lucastliu/sciencebot/dev_ws/src/PlotJuggler/docs/images/pj-area-zoom.gif

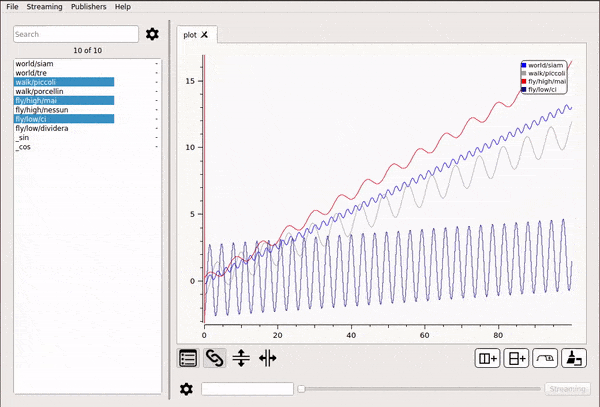
dev_ws/src/PlotJuggler/docs/images/pj-area-zoom.gif
