lucastliu/sciencebot/dev_ws/src/PlotJuggler/docs/images/pj-drag-curve.gif

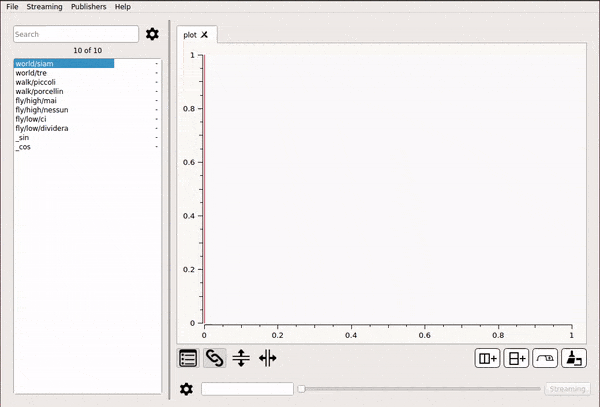
dev_ws/src/PlotJuggler/docs/images/pj-drag-curve.gif
