lucastliu/sciencebot/dev_ws/src/PlotJuggler/docs/images/pj-multiplot.gif

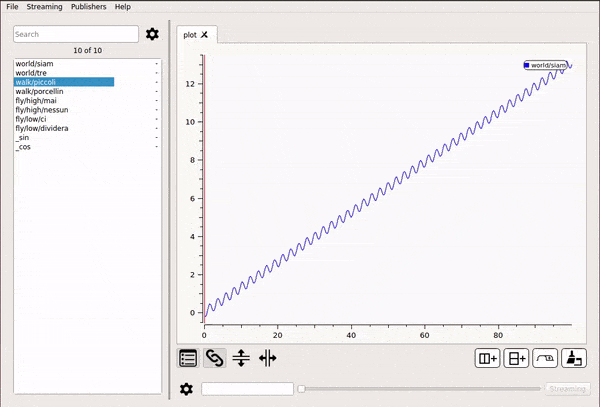
dev_ws/src/PlotJuggler/docs/images/pj-multiplot.gif
