lucastliu/sciencebot/dev_ws/src/PlotJuggler/docs/images/pj-streaming.gif

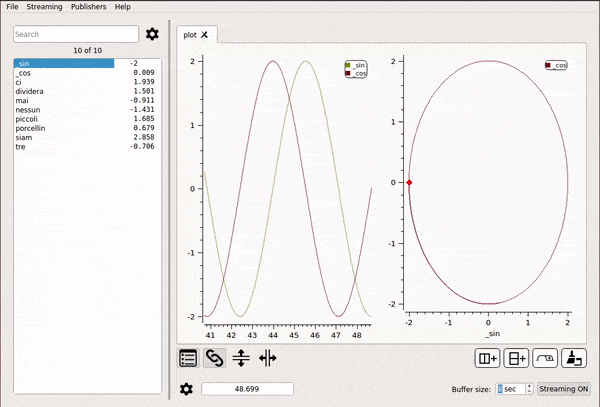
dev_ws/src/PlotJuggler/docs/images/pj-streaming.gif
