lucastliu/sciencebot/dev_ws/src/PlotJuggler/docs/images/pj-streaming.png

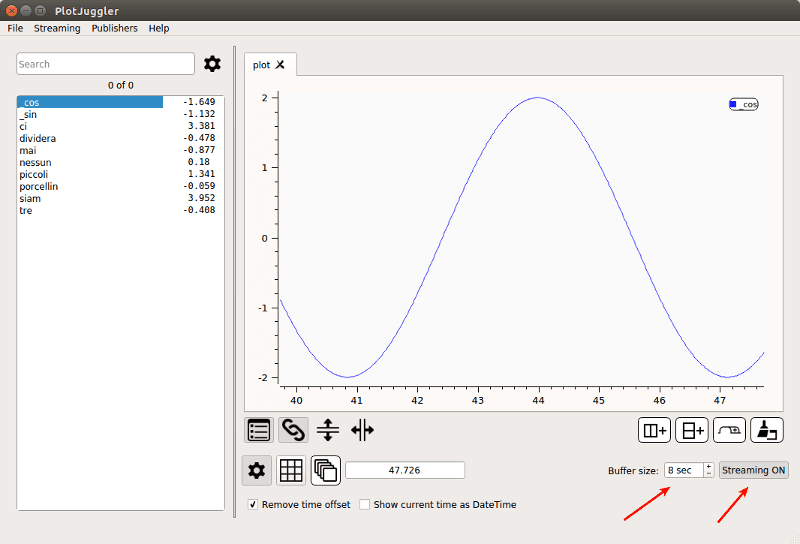
dev_ws/src/PlotJuggler/docs/images/pj-streaming.png
