lucastliu/sciencebot/dev_ws/src/PlotJuggler/docs/images/pj-swap-plots.gif

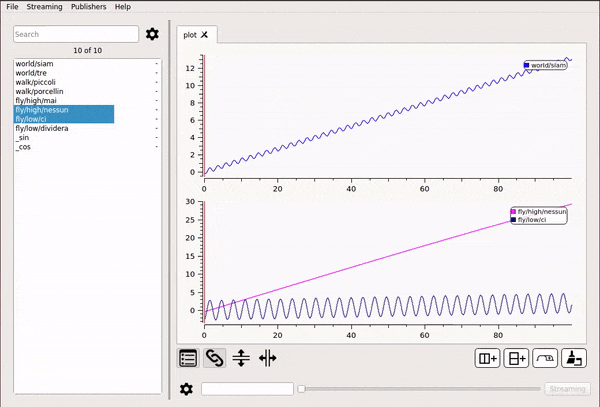
dev_ws/src/PlotJuggler/docs/images/pj-swap-plots.gif
