lucastliu/sciencebot/dev_ws/src/PlotJuggler/docs/images/pj-wheel-zoom.gif

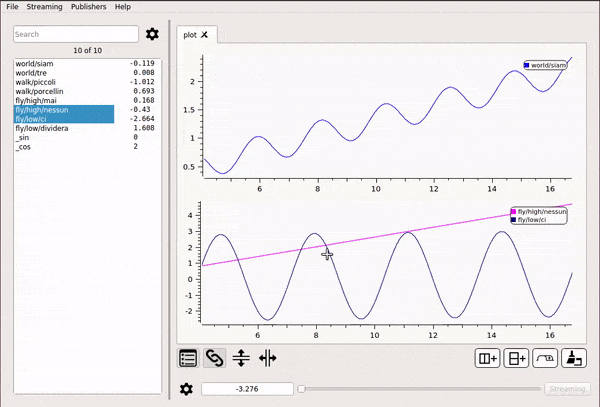
dev_ws/src/PlotJuggler/docs/images/pj-wheel-zoom.gif
