lucastliu/sciencebot/dev_ws/src/PlotJuggler/docs/images/pj-xyplots.gif

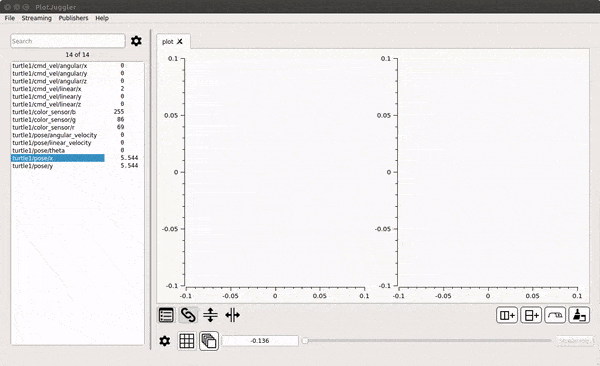
dev_ws/src/PlotJuggler/docs/images/pj-xyplots.gif
