lucastliu/sciencebot/dev_ws/src/PlotJuggler/docs/images/PlotJuggler_terms.png

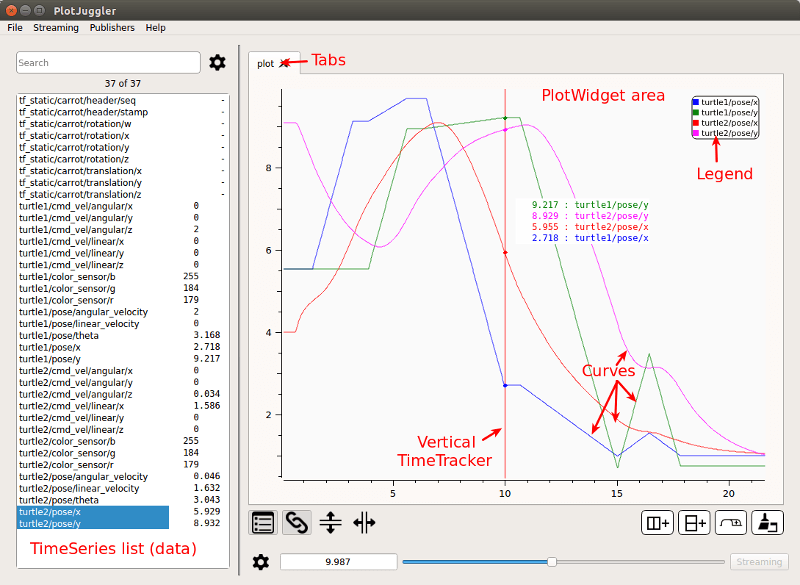
dev_ws/src/PlotJuggler/docs/images/PlotJuggler_terms.png
