lucastliu/sciencebot/dev_ws/src/PlotJuggler/docs/images/PlotJuggler_tracker.png

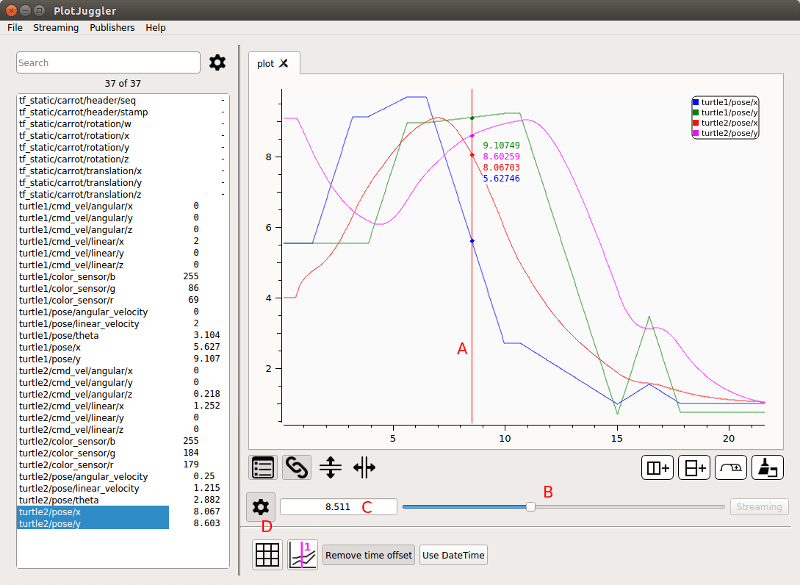
dev_ws/src/PlotJuggler/docs/images/PlotJuggler_tracker.png
