lucastliu/sciencebot/dev_ws/src/PlotJuggler/docs/images/ros-console.png

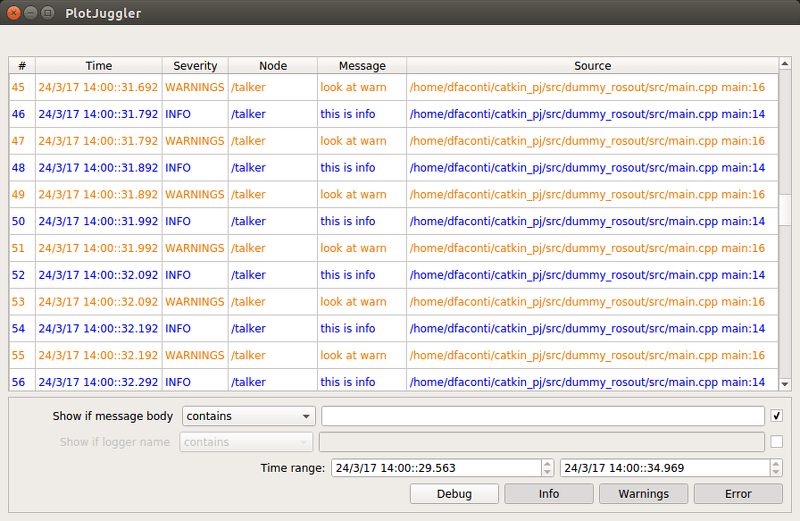
dev_ws/src/PlotJuggler/docs/images/ros-console.png
