lucastliu/sciencebot/dev_ws/src/PlotJuggler/docs/images/ros-topics.png

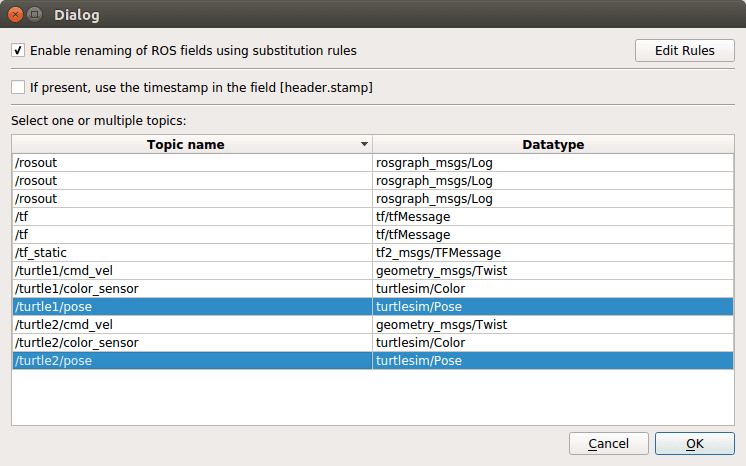
dev_ws/src/PlotJuggler/docs/images/ros-topics.png
