lucastliu/sciencebot/dev_ws/src/PlotJuggler/docs/images/show_me_the_rosbag.jpg

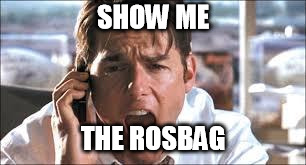
dev_ws/src/PlotJuggler/docs/images/show_me_the_rosbag.jpg
