lucastliu/sciencebot/dev_ws/src/PlotJuggler/plotter_gui/resources/Davide.jpg

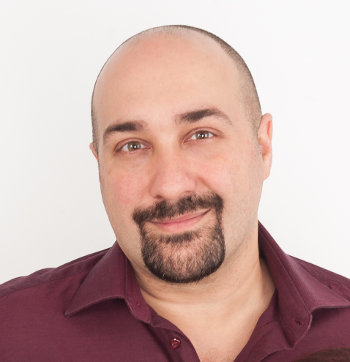
dev_ws/src/PlotJuggler/plotter_gui/resources/Davide.jpg
