lucastliu/sciencebot/dev_ws/src/PlotJuggler/plotter_gui/resources/github.png

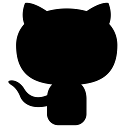
dev_ws/src/PlotJuggler/plotter_gui/resources/github.png
