lucastliu/sciencebot/dev_ws/src/PlotJuggler/plotter_gui/resources/memes/meme_07.jpg

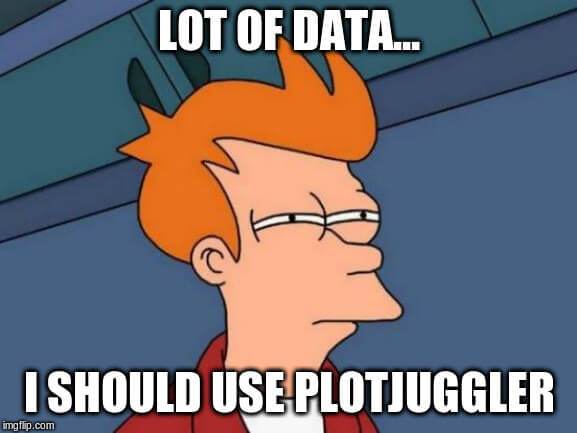
dev_ws/src/PlotJuggler/plotter_gui/resources/memes/meme_07.jpg
