lucastliu/sciencebot/dev_ws/src/PlotJuggler/plotter_gui/resources/memes/meme_08.jpg

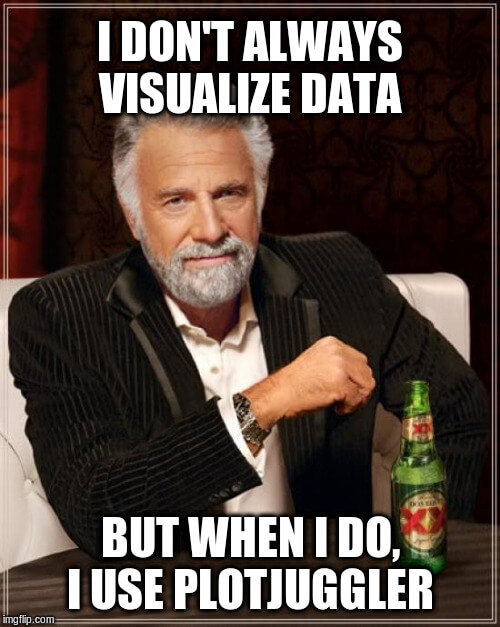
dev_ws/src/PlotJuggler/plotter_gui/resources/memes/meme_08.jpg
