lucastliu/sciencebot/dev_ws/src/PlotJuggler/plotter_gui/resources/memes/meme_19.jpg

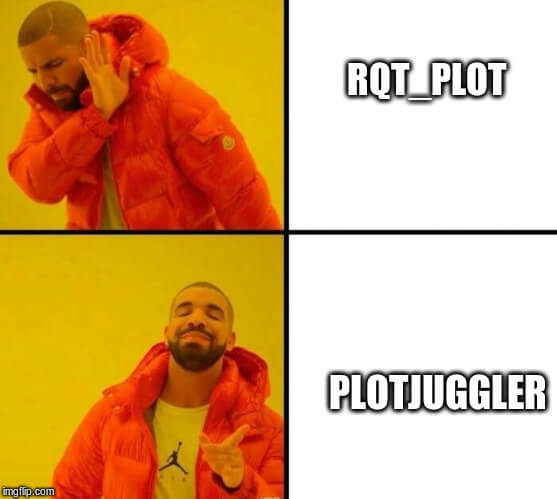
dev_ws/src/PlotJuggler/plotter_gui/resources/memes/meme_19.jpg
