lucastliu/sciencebot/dev_ws/src/PlotJuggler/plotter_gui/resources/memes/meme_21.jpg

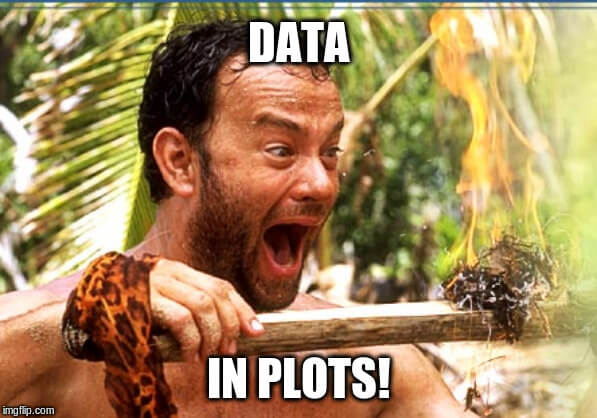
dev_ws/src/PlotJuggler/plotter_gui/resources/memes/meme_21.jpg
