lucastliu/sciencebot/dev_ws/src/PlotJuggler/plotter_gui/resources/memes/meme_22.jpg

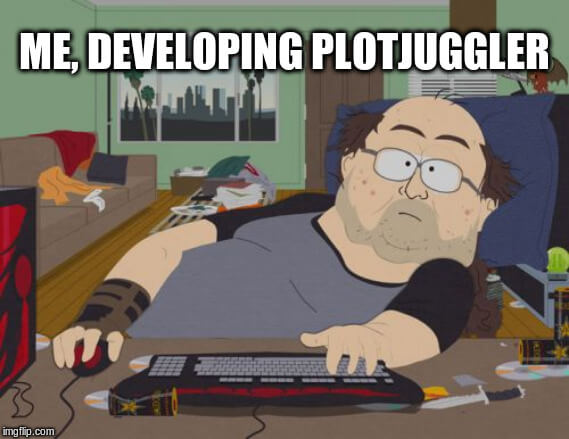
dev_ws/src/PlotJuggler/plotter_gui/resources/memes/meme_22.jpg
