lucastliu/sciencebot/dev_ws/src/PlotJuggler/plotter_gui/resources/memes/meme_39.jpg

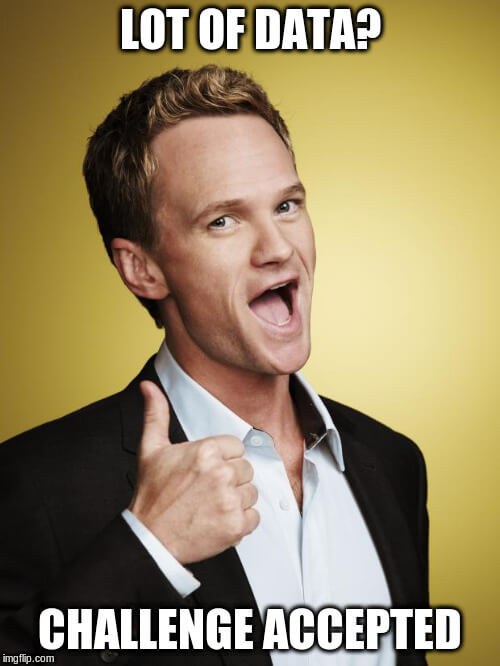
dev_ws/src/PlotJuggler/plotter_gui/resources/memes/meme_39.jpg
