lucastliu/sciencebot/dev_ws/src/PlotJuggler/plotter_gui/resources/memes/meme_44.jpg

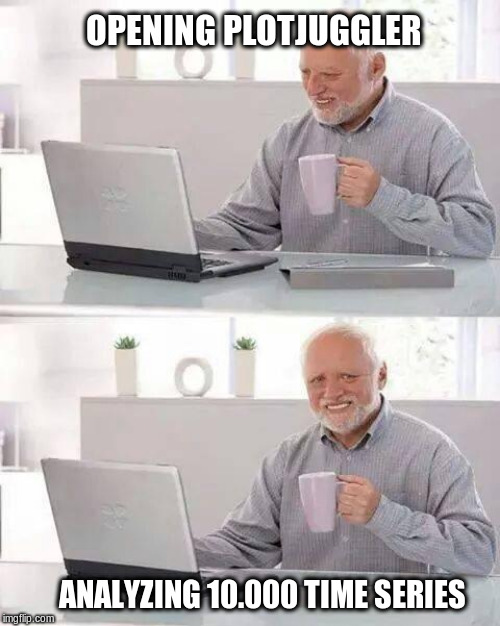
dev_ws/src/PlotJuggler/plotter_gui/resources/memes/meme_44.jpg
