lucastliu/sciencebot/dev_ws/src/PlotJuggler/plotter_gui/resources/memes/meme_48.jpg

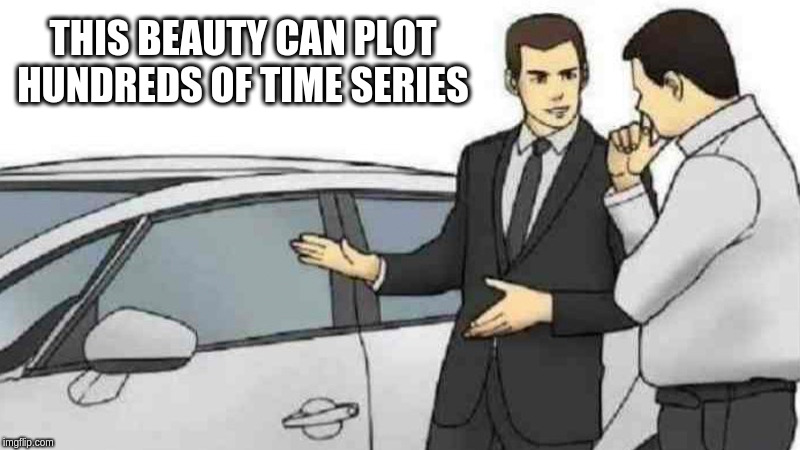
dev_ws/src/PlotJuggler/plotter_gui/resources/memes/meme_48.jpg
