lucastliu/sciencebot/dev_ws/src/PlotJuggler/plotter_gui/resources/memes/meme_52.jpg

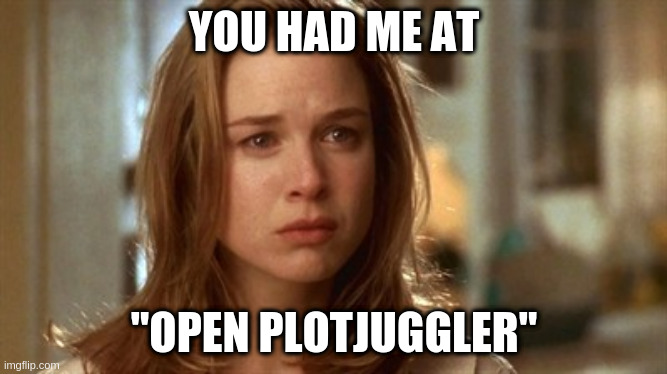
dev_ws/src/PlotJuggler/plotter_gui/resources/memes/meme_52.jpg
