lucastliu/sciencebot/dev_ws/src/PlotJuggler/plotter_gui/resources/memes/meme_60.jpg

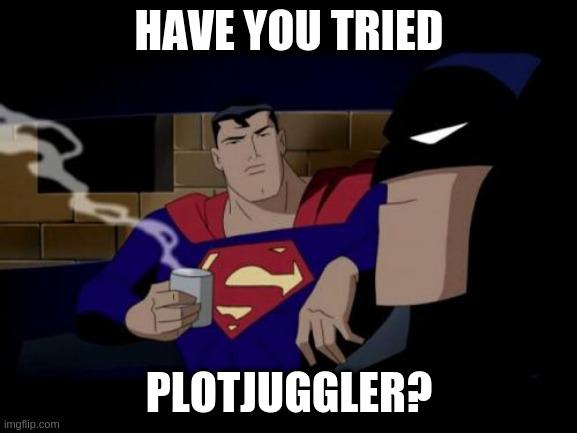
dev_ws/src/PlotJuggler/plotter_gui/resources/memes/meme_60.jpg
