lucastliu/sciencebot/dev_ws/src/PlotJuggler/plotter_gui/resources/twitter.png

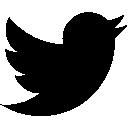
dev_ws/src/PlotJuggler/plotter_gui/resources/twitter.png
