lucastliu/sciencebot/dev_ws/src/PlotJuggler/plotter_gui/resources/update_plotjuggler.jpg

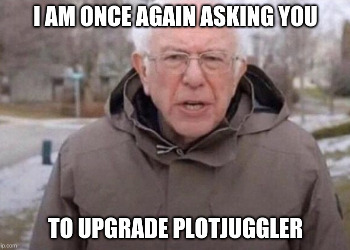
dev_ws/src/PlotJuggler/plotter_gui/resources/update_plotjuggler.jpg
