lucastliu/sciencebot/dev_ws/src/PlotJuggler/plotter_gui/style_dark/add_column.png

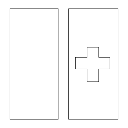
dev_ws/src/PlotJuggler/plotter_gui/style_dark/add_column.png
