lucastliu/sciencebot/dev_ws/src/PlotJuggler/plotter_gui/style_dark/datetime.png

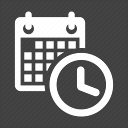
dev_ws/src/PlotJuggler/plotter_gui/style_dark/datetime.png
