lucastliu/sciencebot/dev_ws/src/PlotJuggler/plotter_gui/style_dark/loop.png

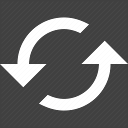
dev_ws/src/PlotJuggler/plotter_gui/style_dark/loop.png
