lucastliu/sciencebot/dev_ws/src/PlotJuggler/plotter_gui/style_dark/pause.png

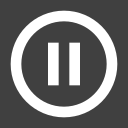
dev_ws/src/PlotJuggler/plotter_gui/style_dark/pause.png
