lucastliu/sciencebot/dev_ws/src/PlotJuggler/plotter_gui/style_dark/play_arrow.png

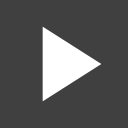
dev_ws/src/PlotJuggler/plotter_gui/style_dark/play_arrow.png
