lucastliu/sciencebot/dev_ws/src/PlotJuggler/plotter_gui/style_dark/point_chart.png

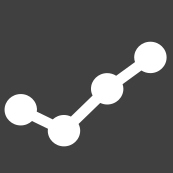
dev_ws/src/PlotJuggler/plotter_gui/style_dark/point_chart.png
