lucastliu/sciencebot/dev_ws/src/PlotJuggler/plotter_gui/style_dark/ratio.png

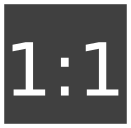
dev_ws/src/PlotJuggler/plotter_gui/style_dark/ratio.png
