lucastliu/sciencebot/dev_ws/src/PlotJuggler/plotter_gui/style_dark/save.png

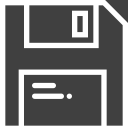
dev_ws/src/PlotJuggler/plotter_gui/style_dark/save.png
