lucastliu/sciencebot/dev_ws/src/PlotJuggler/plotter_gui/style_dark/settings_cog.png

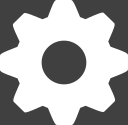
dev_ws/src/PlotJuggler/plotter_gui/style_dark/settings_cog.png
