lucastliu/sciencebot/dev_ws/src/PlotJuggler/plotter_gui/style_dark/zoom_horizontal.png

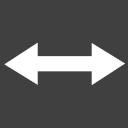
dev_ws/src/PlotJuggler/plotter_gui/style_dark/zoom_horizontal.png
