lucastliu/sciencebot/dev_ws/src/PlotJuggler/plotter_gui/style_dark/zoom_max.png

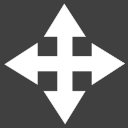
dev_ws/src/PlotJuggler/plotter_gui/style_dark/zoom_max.png
