lucastliu/sciencebot/dev_ws/src/PlotJuggler/plotter_gui/style_light/add_column.png

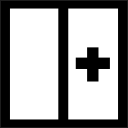
dev_ws/src/PlotJuggler/plotter_gui/style_light/add_column.png
