lucastliu/sciencebot/dev_ws/src/PlotJuggler/plotter_gui/style_light/colored_charts.png

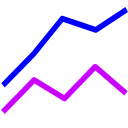
dev_ws/src/PlotJuggler/plotter_gui/style_light/colored_charts.png
