lucastliu/sciencebot/dev_ws/src/PlotJuggler/plotter_gui/style_light/datetime.png

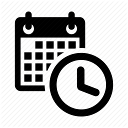
dev_ws/src/PlotJuggler/plotter_gui/style_light/datetime.png
