lucastliu/sciencebot/dev_ws/src/PlotJuggler/plotter_gui/style_light/loop.png

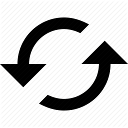
dev_ws/src/PlotJuggler/plotter_gui/style_light/loop.png
