lucastliu/sciencebot/dev_ws/src/PlotJuggler/plotter_gui/style_light/pause.png

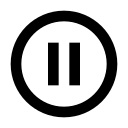
dev_ws/src/PlotJuggler/plotter_gui/style_light/pause.png
