lucastliu/sciencebot/dev_ws/src/PlotJuggler/plotter_gui/style_light/play_arrow.png

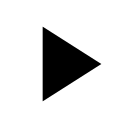
dev_ws/src/PlotJuggler/plotter_gui/style_light/play_arrow.png
