lucastliu/sciencebot/dev_ws/src/PlotJuggler/plotter_gui/style_light/point_chart.png

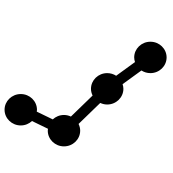
dev_ws/src/PlotJuggler/plotter_gui/style_light/point_chart.png
