lucastliu/sciencebot/dev_ws/src/PlotJuggler/plotter_gui/style_light/ratio.png

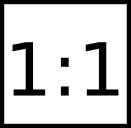
dev_ws/src/PlotJuggler/plotter_gui/style_light/ratio.png
