lucastliu/sciencebot/dev_ws/src/PlotJuggler/plotter_gui/style_light/remove_list.png

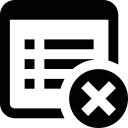
dev_ws/src/PlotJuggler/plotter_gui/style_light/remove_list.png
