lucastliu/sciencebot/dev_ws/src/PlotJuggler/plotter_gui/style_light/save.png

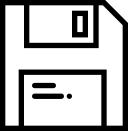
dev_ws/src/PlotJuggler/plotter_gui/style_light/save.png
