lucastliu/sciencebot/dev_ws/src/PlotJuggler/plotter_gui/style_light/settings_cog.png

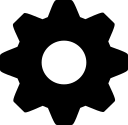
dev_ws/src/PlotJuggler/plotter_gui/style_light/settings_cog.png
