lucastliu/sciencebot/dev_ws/src/PlotJuggler/plotter_gui/style_light/zoom_horizontal.png

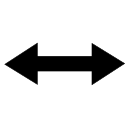
dev_ws/src/PlotJuggler/plotter_gui/style_light/zoom_horizontal.png
