lucastliu/sciencebot/dev_ws/src/PlotJuggler/plotter_gui/style_light/zoom_vertical.png

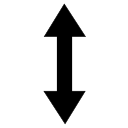
dev_ws/src/PlotJuggler/plotter_gui/style_light/zoom_vertical.png
