lucastliu/sciencebot/images/bot.png

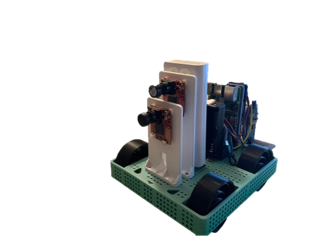
images/bot.png
