lucastliu/sciencebot/images/botfront.png

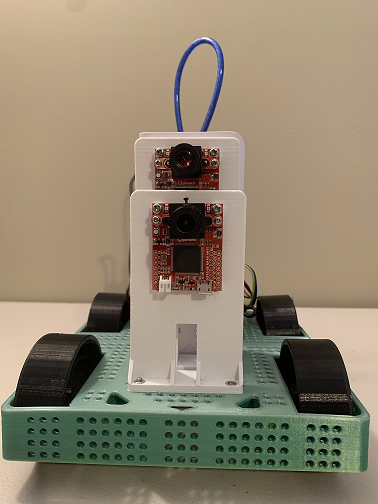
images/botfront.png
