lucastliu/sciencebot/images/case.png

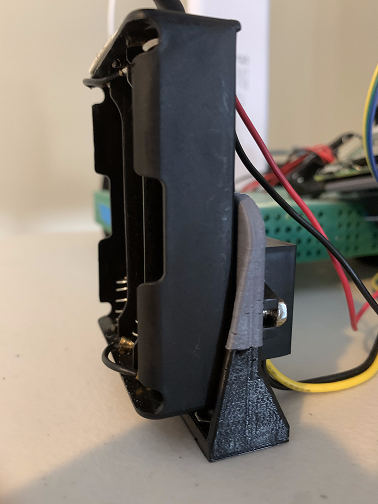
images/case.png
