lucastliu/sciencebot/images/screenshot.png

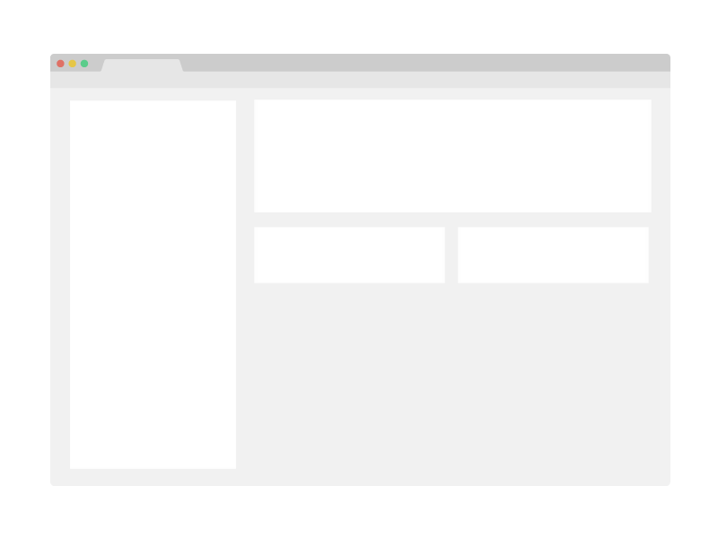
images/screenshot.png
