lucastliu/sciencebot/images/turtles.png

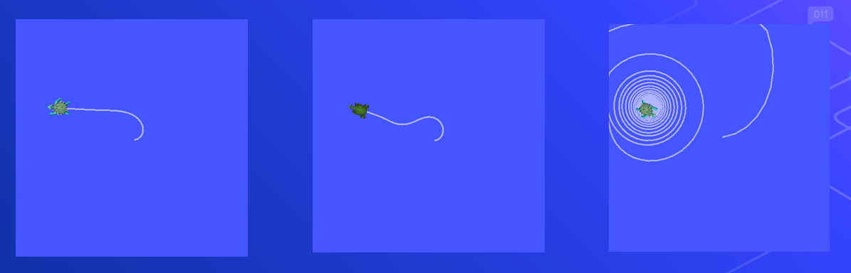
images/turtles.png
