lucastliu/sciencebot/camera/eTaxi_Lucas.py

import math
from eTaxiBase import eTaxiBase
from motorController import motorController
import threading
import time

from H7Camera import H7Camera


class eTaxi_Lucas(eTaxiBase):
    # Error Vars
    MAX_POS_ERROR = 10
    MAX_IMU_ERROR_DEG = 0.05
    MAX_IMU_ERROR = (MAX_IMU_ERROR_DEG / 360) * 2 * math.pi

    TURN_SPEED = 50
    MOVE_SPEED = -80

    heading = 0.0

    motors = None

    def __init__(self):
        self.motors = motorController()
        self.heading = 0

        # None of this works and we don't know why
        # self.cameras = []
        # self.cameras.append(H7Camera(port_name="/dev/ttyACM0"))
        #self.cameras.append(H7Camera(port_name="/dev/ttyACM1"))
        # MV_thread = threading.Thread(target=self.update_openMV)
        # MV_thread.start()

        print('eTaxi_Lucas Initialized')

    def get_position(self):
        position = self.myTag.get_pos()
        return position[0], position[1]

    def move(self, dist_cm):
        dist_m = dist_cm/100
        self.motors.move(dist_m, self.MOVE_SPEED)

    def turn_to_heading(self, rads):
        delta = self.angle_between_headings(math.radians(self.heading), rads)
        print('turn_to_heading_delta: ', delta)
        if delta < 0:
            self.motors.turnRight(math.degrees(abs(delta)), self.TURN_SPEED)
        else:
            self.motors.turnLeft(math.degrees(abs(delta)), self.TURN_SPEED)
        self.heading = rads

    def turnRight(self, rads):
        self.motors.turnRight(math.degrees(abs(rads)), self.TURN_SPEED)
        self.heading = self.heading - rads

    def turnLeft(self, rads):
        self.motors.turnLeft(math.degrees(abs(rads)), self.TURN_SPEED)
        self.heading = self.heading + rads


    def get_motors(self):
        return self.motors

    def get_heading(self):
        return self.heading

    # def update_openMV(self):
    #     while True:
    #         for camera in self.cameras:
    #             time.sleep(3)
    #             camera.update()
    #             camera.update_thread_test()
    #             time.sleep(3)
    #             camera.update_test()
    #             time.sleep(3)
    #             camera.update_tag_present()
    #             time.sleep(3)
